max-verem/stm32_ltc_encoder/firmware/Core/Inc/font-12x16.h

#ifndef font_12x16_h
#define font_12x16_h

static const unsigned char console_font_12x16[] =
{
    /*
     * code=48, hex=0x30, ascii="0"
     */
    0x0F,0x80,  /* 000011111000 */
    0x3F,0xE0,  /* 001111111110 */
    0x30,0x60,  /* 001100000110 */
    0x60,0x70,  /* 011000000111 */
    0x60,0xF0,  /* 011000001111 */
    0x61,0xB0,  /* 011000011011 */
    0x63,0x30,  /* 011000110011 */
    0x66,0x30,  /* 011001100011 */
    0x6C,0x30,  /* 011011000011 */
    0x78,0x30,  /* 011110000011 */
    0x70,0x30,  /* 011100000011 */
    0x30,0x60,  /* 001100000110 */
    0x3F,0xE0,  /* 001111111110 */
    0x0F,0x80,  /* 000011111000 */
    0x00,0x00,  /* 000000000000 */
    0x00,0x00,  /* 000000000000 */

    /*
     * code=49, hex=0x31, ascii="1"
     */
    0x03,0x00,  /* 000000110000 */
    0x07,0x00,  /* 000001110000 */
    0x1F,0x00,  /* 000111110000 */
    0x1F,0x00,  /* 000111110000 */
    0x03,0x00,  /* 000000110000 */
    0x03,0x00,  /* 000000110000 */
    0x03,0x00,  /* 000000110000 */
    0x03,0x00,  /* 000000110000 */
    0x03,0x00,  /* 000000110000 */
    0x03,0x00,  /* 000000110000 */
    0x03,0x00,  /* 000000110000 */
    0x03,0x00,  /* 000000110000 */
    0x1F,0xE0,  /* 000111111110 */
    0x1F,0xE0,  /* 000111111110 */
    0x00,0x00,  /* 000000000000 */
    0x00,0x00,  /* 000000000000 */

    /*
     * code=50, hex=0x32, ascii="2"
     */
    0x1F,0xC0,  /* 000111111100 */
    0x3F,0xE0,  /* 001111111110 */
    0x70,0x70,  /* 011100000111 */
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
    0x07,0x80,  /* 000001111000 */
    0x03,0x80,  /* 000000111000 */
    0x01,0x80,  /* 000000011000 */
    0x00,0x80,  /* 000000001000 */
    0x00,0x00,  /* 000000000000 */
    0x00,0x00,  /* 000000000000 */
    0x00,0x00,  /* 000000000000 */
};

#endif /* font_12x16_h */
